p4nic4ttack/Ages/Pictures/367420182_779549450583015_961303321797435456_n.jpg

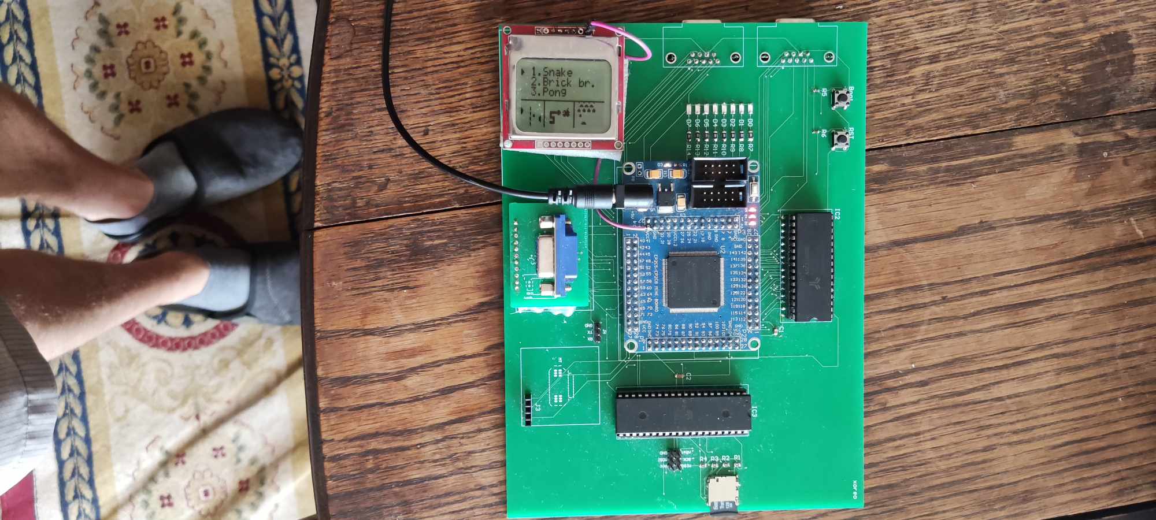
Pictures/367420182_779549450583015_961303321797435456_n.jpg
