p4nic4ttack/Ages/Pictures/inline-asm.png

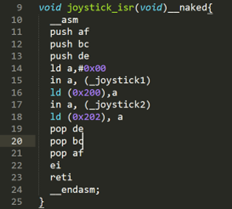
Pictures/inline-asm.png
