p4nic4ttack/Ages/Pictures/led-matrix-chain.png

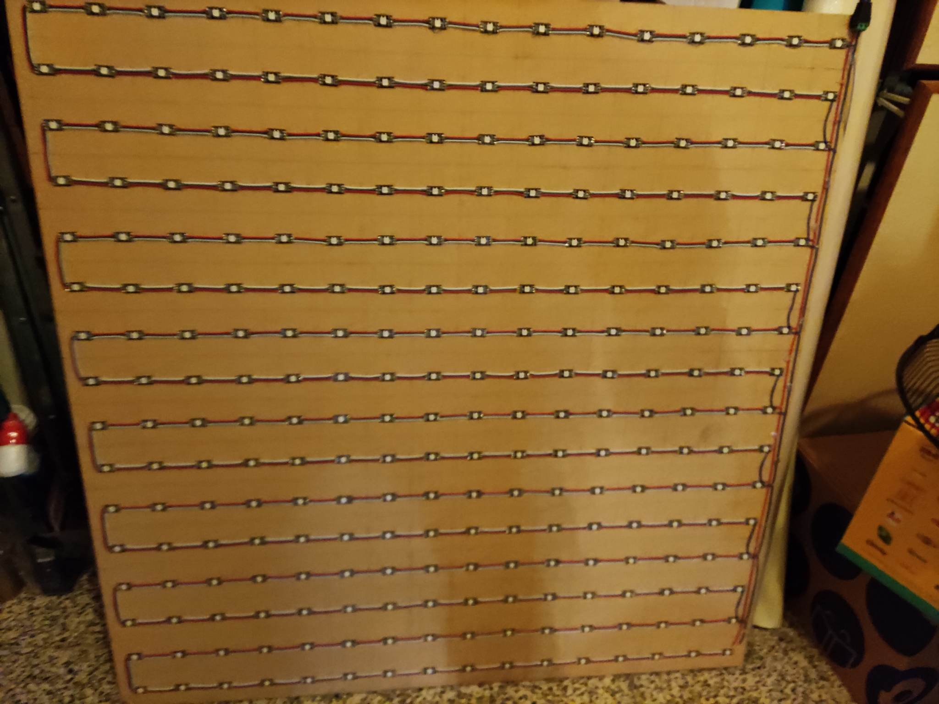
Pictures/led-matrix-chain.png
