p4nic4ttack/Ages/Pictures/pong-scores.jpg

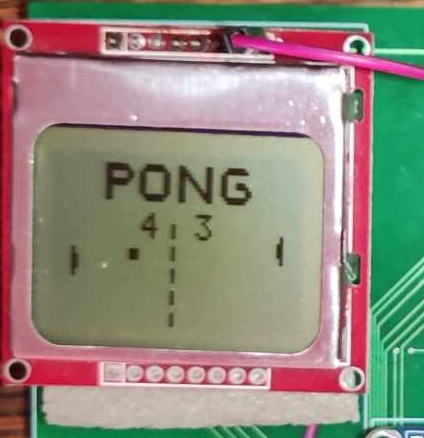
Pictures/pong-scores.jpg
