p4nic4ttack/Ages/Pictures/snake-score.jpg

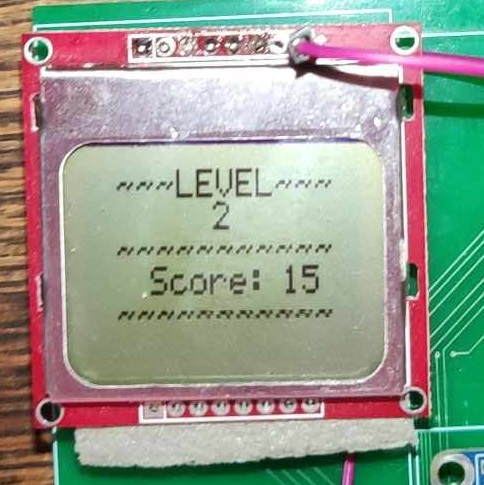
Pictures/snake-score.jpg
