p4nic4ttack/Ages/Pictures/vga2.jpg

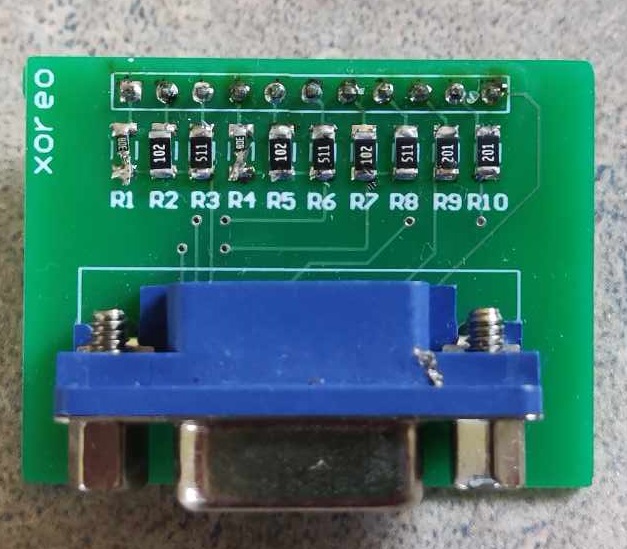
Pictures/vga2.jpg
